Keitark/fc-rom-vomitter/firmware/main/app_main.c

#include "controller.h"
#include "ap_rx_trace.h"
#include "esp_check.h"
#include "esp_log.h"
#include "nvs_flash.h"
#include "nes_sdr_platform.h"
#include "freertos/FreeRTOS.h"
#include "freertos/task.h"
#include "usb_loader.h"
#include "web_server.h"

static const char *TAG = "rom_vomitter";

void app_main(void)
{
    ESP_ERROR_CHECK(ap_rx_trace_init());
    esp_err_t err = nvs_flash_init();
    if (err == ESP_ERR_NVS_NO_FREE_PAGES || err == ESP_ERR_NVS_NEW_VERSION_FOUND) {
        ESP_ERROR_CHECK(nvs_flash_erase());
        err = nvs_flash_init();
    }
    ESP_ERROR_CHECK(err);
    ESP_ERROR_CHECK(controller_init());
    ESP_ERROR_CHECK(usb_loader_start());
    ESP_ERROR_CHECK(web_server_start());
    ESP_LOGI(TAG, "firmware prepared; hardware validation pending board arrival");
    /* Normally the resident USB task handles exclusive SDR startup. */
    if (!usb_loader_enabled()) {
        for (;;) {
            nes_sdr_platform_service_rf_start();
            vTaskDelay(pdMS_TO_TICKS(250));
        }
    }
}
